elktownlabs/murgcam/web-backend/refphotos/low.jpeg

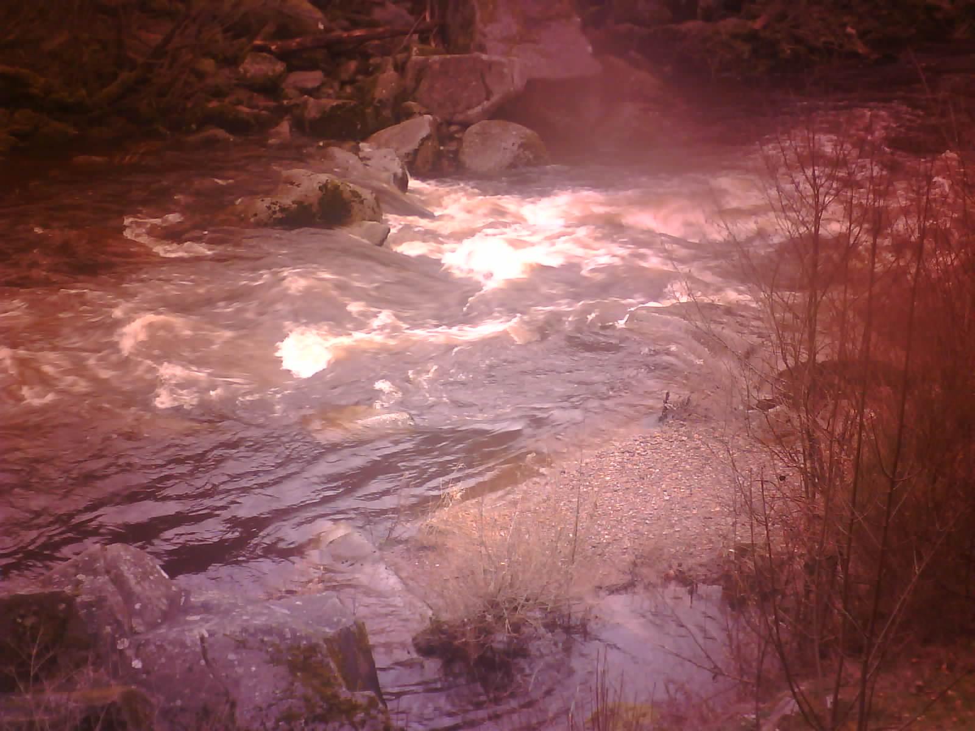
web-backend/refphotos/low.jpeg
