elktownlabs/murgcam/cad/optics/aliexpress-order-csmount-lens-holder.png

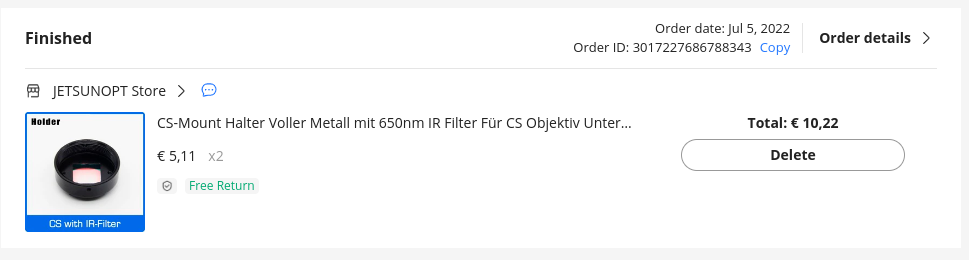
cad/optics/aliexpress-order-csmount-lens-holder.png
