elktownlabs/murgcam/cad/optics/aliexpress-order-csmount-zoom-lens.png

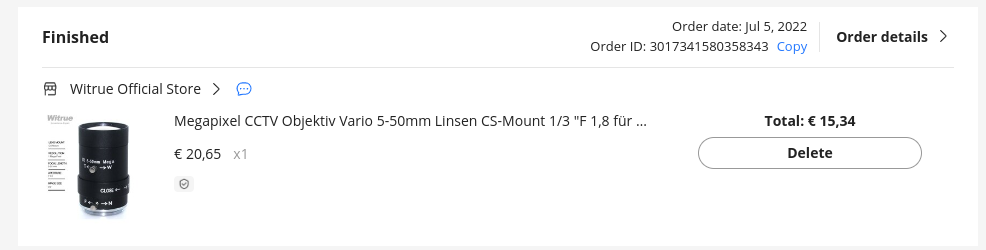
cad/optics/aliexpress-order-csmount-zoom-lens.png
