elktownlabs/murgcam/cad/enclosure_narrow/base_narrow_cam/bolts/common/version.scad

function BOLTS_version() = [0, 3, "LGPL 2.1+"];
function BOLTS_date() = [2014,4,24];
function BOLTS_license() = "LGPL 2.1+";
