elktownlabs/murgcam/firmware/elkcam_firmware/main/webserver.c

#include "webserver.h"
#include "esp_http_server.h"
#include "esp_log.h"
#include "events.h"
#include "gpios.h"
#include "cJSON.h"
#include "cam.h"
#include "camhandler.h"
#include "configstorage.h"

static const char *TAG = "httpserver";

unsigned char index_html_gz[] = {
  0x1f, 0x8b, 0x08, 0x08, 0xf7, 0x94, 0x00, 0x61, 0x00, 0x03, 0x69, 0x6e,
  0x64, 0x65, 0x78, 0x2e, 0x68, 0x74, 0x6d, 0x6c, 0x00, 0xed, 0x5c, 0x6d,
  0x73, 0xdb, 0x36, 0x12, 0xfe, 0x9e, 0x5f, 0x81, 0x32, 0x6d, 0x25, 0xf7,
  0x4c, 0x59, 0xb2, 0x9d, 0xc4, 0x91, 0x2d, 0xf5, 0x9c, 0x34, 0x77, 0xe9,
  0x4d, 0x9a, 0xf8, 0xea, 0xbe, 0xdc, 0x4d, 0xa7, 0xe3, 0x42, 0x24, 0x28,
  0xb1, 0x26, 0x09, 0x16, 0x00, 0x65, 0xbb, 0x19, 0xff, 0xf7, 0x5b, 0x00,
  0x24, 0x05, 0x50, 0xa0, 0x4c, 0xa5, 0xae, 0xa7, 0xbd, 0x3b, 0x69, 0x26,
  0x26, 0x09, 0xec, 0x2e, 0x76, 0xf7, 0xd9, 0xc5, 0x02, 0xa0, 0x72, 0xb2,
  0x10, 0x69, 0x32, 0x7d, 0x84, 0xd0, 0xc9, 0x82, 0xe0, 0x50, 0x5e, 0xc0,
  0x65, 0x4a, 0x04, 0x46, 0xc1, 0x02, 0x33, 0x4e, 0xc4, 0xc4, 0x2b, 0x44,
  0xe4, 0x1f, 0x79, 0x66, 0x53, 0x86, 0x53, 0x32, 0xf1, 0x96, 0x31, 0xb9,
  0xca, 0x29, 0x13, 0x1e, 0x0a, 0x68, 0x26, 0x48, 0x06, 0x5d, 0xaf, 0xe2,
  0x50, 0x2c, 0x26, 0x21, 0x59, 0xc6, 0x01, 0xf1, 0xd5, 0xcd, 0x6e, 0x9c,
  0xc5, 0x22, 0xc6, 0x89, 0xcf, 0x03, 0x9c, 0x90, 0xc9, 0xa8, 0xe2, 0x23,
  0x62, 0x91, 0x90, 0xe9, 0xab, 0xe4, 0x32, 0xc0, 0xe9, 0xc9, 0x9e, 0xbe,
  0xd3, 0x2d, 0x5c, 0xdc, 0x54, 0xd7, 0xf2, 0xb3, 0xf7, 0x59, 0x7d, 0xf9,
  0x19, 0x7a, 0x79, 0x7e, 0x8e, 0x22, 0xca, 0x90, 0x58, 0x10, 0x44, 0x78,
  0x7e, 0xb0, 0x8f, 0x80, 0x1c, 0x5d, 0x91, 0x19, 0x27, 0x6c, 0x49, 0xd8,
  0xaa, 0xe7, 0x5e, 0x7d, 0x39, 0xa3, 0xe1, 0x0d, 0x7a, 0x5f, 0xdf, 0x46,
  0x30, 0x54, 0x3f, 0xc2, 0x69, 0x9c, 0xdc, 0x8c, 0xd1, 0x29, 0x83, 0x91,
  0xed, 0xbe, 0x26, 0xc9, 0x92, 0x88, 0x38, 0xc0, 0xbb, 0x1c, 0x67, 0xdc,
  0x07, 0x56, 0x71, 0x74, 0xbc, 0xa2, 0xc7, 0xc1, 0xe5, 0x9c, 0xd1, 0x22,
  0x0b, 0xc7, 0xe8, 0xf1, 0xe8, 0x48, 0x7e, 0x57, 0x8d, 0x01, 0x4d, 0x28,
  0x83, 0xe7, 0xaf, 0xfe, 0x26, 0xbf, 0xc7, 0xb6, 0x14, 0x1e, 0xff, 0x4a,
  0xc6, 0x68, 0xf4, 0x34, 0xbf, 0xae, 0x9f, 0xdf, 0xd6, 0x57, 0xd8, 0x18,
  0x53, 0x1b, 0x17, 0x41, 0xae, 0x85, 0x1f, 0x92, 0x80, 0x32, 0x2c, 0x62,
  0x9a, 0x8d, 0x11, 0x0c, 0x82, 0xb0, 0x24, 0xce, 0x88, 0x83, 0xe1, 0x62,
  0xbf, 0xa9, 0x65, 0x29, 0xff, 0xc8, 0x29, 0x9f, 0x93, 0x40, 0xf2, 0x1c,
  0xa4, 0x38, 0xce, 0x0c, 0xc2, 0x30, 0xe6, 0x79, 0x82, 0xc1, 0x34, 0x51,
  0x42, 0x5c, 0x64, 0x8f, 0x53, 0x92, 0x15, 0xbb, 0x2d, 0xc4, 0x92, 0xc6,
  0x0f, 0x63, 0xa6, 0x5b, 0xc7, 0x52, 0xaf, 0x22, 0xcd, 0xda, 0xb8, 0xb8,
  0xa4, 0x66, 0x34, 0x23, 0xc7, 0x36, 0xbf, 0x2b, 0x86, 0x73, 0xd9, 0x20,
  0xff, 0xae, 0x9a, 0x14, 0xb6, 0xc6, 0xe8, 0xe0, 0x68, 0x98, 0x5f, 0xb7,
  0xf8, 0xea, 0xe0, 0xa9, 0xfc, 0xae, 0x1a, 0x73, 0x1c, 0x86, 0x71, 0x36,
  0x1f, 0xa3, 0x23, 0x8b, 0x84, 0x32, 0xb0, 0xa9, 0xcf, 0x70, 0x18, 0x17,
  0x7c, 0x8c, 0x0e, 0xcd, 0xb6, 0x14, 0xb3, 0x79, 0x9c, 0xf9, 0x82, 0xc2,
  0x00, 0xfc, 0xd1, 0xd0, 0xd1, 0xc4, 0xe2, 0xf9, 0x42, 0x80, 0x8d, 0xad,
  0xb6, 0x5b, 0x03, 0xbb, 0x5a, 0xdd, 0x32, 0x3e, 0xda, 0xec, 0xec, 0xd4,
  0xd8, 0xd6, 0x17, 0x27, 0xf1, 0x3c, 0xf3, 0x63, 0x41, 0x52, 0x18, 0x24,
  0x17, 0x8c, 0x88, 0x60, 0xe1, 0x10, 0x68, 0xe0, 0x3e, 0x8a, 0xe7, 0x05,
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
};
unsigned int index_html_gz_len = 3640;


/* An HTTP GET handler */
static esp_err_t photo_get_handler(httpd_req_t *req)
{
    char*  buf;
    size_t buf_len;

    /* Get header value string length and allocate memory for length + 1,
     * extra byte for null termination */
    buf_len = httpd_req_get_hdr_value_len(req, "Host") + 1;
    if (buf_len > 1) {
        buf = malloc(buf_len);
        /* Copy null terminated value string into buffer */
        if (httpd_req_get_hdr_value_str(req, "Host", buf, buf_len) == ESP_OK) {
            ESP_LOGI(TAG, "Host %s requested a picture.", buf);
        }
        free(buf);
    }


    uint8_t *cam_buf = NULL;

    ESP_LOGI(TAG, "Taking picture");
    reinit_cam();
    camhandler_load_config_from_nvs();
    cam_start();
    size_t data_len = cam_take(&cam_buf, 8000 / portTICK_PERIOD_MS);
    cam_stop();
    if (data_len == 0) {
        ESP_LOGE(TAG, "Camera timed out");
        cam_give(cam_buf);
        return ESP_OK;
    }
    /* find end of jpeg stream and truncate data there */
    for (uint32_t i=0; i<data_len-1; i++) {
        if (cam_buf[i] == 0xff && cam_buf[i+1] == 0xd9) {
            ESP_LOGI(TAG, "Shortened data from %d to %d.", data_len, i+2);
            data_len = i+2;
            break;
        }
    }
    ESP_LOGI(TAG, "Picture taken. Size = %d", data_len);

    /* Set some custom headers */
    httpd_resp_set_hdr(req, "Content-Type", "image/jpeg");

    /* Send response with custom headers and body set as the
     * string passed in user context*/
    httpd_resp_send(req, (const char*)cam_buf, data_len);

    cam_give(cam_buf);

    /* After sending the HTTP response the old HTTP request
     * headers are lost. Check if HTTP request headers can be read now. */
    if (httpd_req_get_hdr_value_len(req, "Host") == 0) {
        ESP_LOGI(TAG, "Request headers lost");
    }
    return ESP_OK;
}


/* HTTP GET handler for root page (/) */
static esp_err_t index_handler(httpd_req_t *req)
{
    char*  buf;
    size_t buf_len;

    /* Get header value string length and allocate memory for length + 1,
     * extra byte for null termination */
    buf_len = httpd_req_get_hdr_value_len(req, "Host") + 1;
    if (buf_len > 1) {
        buf = malloc(buf_len);
        /* Copy null terminated value string into buffer */
        if (httpd_req_get_hdr_value_str(req, "Host", buf, buf_len) == ESP_OK) {
            ESP_LOGI(TAG, "Host %s requested index.", buf);
        }
        free(buf);
    }

    /* Set some custom headers */
    httpd_resp_set_hdr(req, "Content-Type", "text/html");
    httpd_resp_set_hdr(req, "Content-Encoding" , "gzip");

    httpd_resp_send(req, (const char*)index_html_gz, index_html_gz_len);


    /* After sending the HTTP response the old HTTP request
     * headers are lost. Check if HTTP request headers can be read now. */
    if (httpd_req_get_hdr_value_len(req, "Host") == 0) {
        ESP_LOGI(TAG, "Request headers lost");
    }

    return ESP_OK;
}


/* An HTTP GET handler */
static esp_err_t config_get_handler(httpd_req_t *req)
{
    char*  buf;
    size_t buf_len;
	cJSON *root;

    /* build json configuration */
    root = cJSON_CreateObject();
    camera_config_t* cam_conf = config_cam();
    cell_config_t* cell_conf = config_cell();
    system_config_t* sys_conf = config_system();
    cJSON_AddNumberToObject(root, "cam_quality", cam_conf->quality);
    cJSON_AddNumberToObject(root, "cam_auto_exposure", cam_conf->auto_exposure);
    cJSON_AddNumberToObject(root, "cam_light_mode", cam_conf->light_mode);
    cJSON_AddNumberToObject(root, "cam_color_saturation", cam_conf->color_saturation);
    cJSON_AddNumberToObject(root, "cam_pixeltiming", cam_conf->pixeltiming);
    cJSON_AddNumberToObject(root, "cam_brightness", cam_conf->brightness);
    cJSON_AddNumberToObject(root, "cam_hue", cam_conf->hue);
    cJSON_AddNumberToObject(root, "cam_sharpness", cam_conf->sharpness);
    cJSON_AddNumberToObject(root, "cam_contrast", cam_conf->contrast);
    cJSON_AddStringToObject(root, "cell_pin", cell_conf->pin);
    cJSON_AddStringToObject(root, "cell_apn", cell_conf->apn);
    cJSON_AddStringToObject(root, "cell_apn_user", cell_conf->apn_user);
    cJSON_AddStringToObject(root, "cell_apn_pass", cell_conf->apn_pass);
    cJSON_AddNumberToObject(root, "cell_apn_auth", cell_conf->apn_auth);
    cJSON_AddStringToObject(root, "cell_remote_address", cell_conf->remote_address);
    cJSON_AddStringToObject(root, "cell_remote_url", cell_conf->remote_url);
    cJSON_AddNumberToObject(root, "sys_secs_between_photos", sys_conf->secs_between_photos);
    cJSON_AddNumberToObject(root, "sys_minimum_voltage", sys_conf->min_voltage);

    /* Get header value string length and allocate memory for length + 1,
     * extra byte for null termination */
    buf_len = httpd_req_get_hdr_value_len(req, "Host") + 1;
    if (buf_len > 1) {
        buf = malloc(buf_len);
        /* Copy null terminated value string into buffer */
        if (httpd_req_get_hdr_value_str(req, "Host", buf, buf_len) == ESP_OK) {
            ESP_LOGI(TAG, "Host %s requested configuration.", buf);
        }
        free(buf);
    }

    /* Set some custom headers */
    httpd_resp_set_hdr(req, "Content-Type", "application/json");

    /* Send response with custom headers and body set as the
     * string passed in user context*/
    const char *my_json_string = cJSON_Print(root);
    httpd_resp_send(req, my_json_string, strlen(my_json_string));

    /* free memory */
    cJSON_Delete(root);

    /* After sending the HTTP response the old HTTP request
     * headers are lost. Check if HTTP request headers can be read now. */
    if (httpd_req_get_hdr_value_len(req, "Host") == 0) {
        ESP_LOGI(TAG, "Request headers lost");
    }

    return ESP_OK;
}



/* An HTTP GET handler */
static esp_err_t config_set_handler(httpd_req_t *req)
{
    char content[512];

    /* truncate if content length larger than the buffer */
    size_t recv_size = (req->content_len < sizeof(content)) ? req->content_len : sizeof(content);

    int ret = httpd_req_recv(req, content, recv_size);
    if (ret <= 0) {  /* 0 return value indicates connection closed */
        /* Check if timeout occurred */
        if (ret == HTTPD_SOCK_ERR_TIMEOUT) {
            httpd_resp_send_408(req);
        }
        return ESP_FAIL;
    }

    ESP_LOGI(TAG, "Received set request: %s", content);

    /* parse json */
    cJSON *config_json = cJSON_Parse(content);
    if (config_json == NULL) {
        ESP_LOGE(TAG, "Error parsing json in setconfig post request");
        httpd_resp_send_408(req);
        return ESP_FAIL;
    }

    /* update config storage */
    camera_config_t cam_conf = *(config_cam());
    system_config_t sys_conf = *(config_system());
    cell_config_t cell_conf = *(config_cell());

    cJSON *value;
    value = cJSON_GetObjectItemCaseSensitive(config_json, "cam_quality");
    if (cJSON_IsNumber(value)) {
        ESP_LOGI(TAG, "Setting quality to %d", value->valueint);
        cam_conf.quality = value->valueint;
    }
    value = cJSON_GetObjectItemCaseSensitive(config_json, "cam_auto_exposure");
    if (cJSON_IsNumber(value)) {
        ESP_LOGI(TAG, "Setting auto exposure to %d", value->valueint);
        cam_conf.auto_exposure = value->valueint;
    }
    value = cJSON_GetObjectItemCaseSensitive(config_json, "cam_light_mode");
    if (cJSON_IsNumber(value)) {
        ESP_LOGI(TAG, "Setting light mode to %d", value->valueint);
        cam_conf.light_mode = value->valueint;
    }
    value = cJSON_GetObjectItemCaseSensitive(config_json, "cam_color_saturation");
    if (cJSON_IsNumber(value)) {
        ESP_LOGI(TAG, "Setting saturation to %d", value->valueint);
        cam_conf.color_saturation = value->valueint;
    }
    value = cJSON_GetObjectItemCaseSensitive(config_json, "cam_pixeltiming");
    if (cJSON_IsNumber(value)) {
        ESP_LOGI(TAG, "Setting pixel timing to %d", value->valueint);
        cam_conf.pixeltiming = value->valueint;
    }
    value = cJSON_GetObjectItemCaseSensitive(config_json, "cam_brightness");
    if (cJSON_IsNumber(value)) {
        ESP_LOGI(TAG, "Setting brightness to %d", value->valueint);
        cam_conf.brightness = value->valueint;
    }
    value = cJSON_GetObjectItemCaseSensitive(config_json, "cam_contrast");
    if (cJSON_IsNumber(value)) {
        ESP_LOGI(TAG, "Setting contrast to %d", value->valueint);
        cam_conf.contrast = value->valueint;
    }
    value = cJSON_GetObjectItemCaseSensitive(config_json, "cam_hue");
    if (cJSON_IsNumber(value)) {
        ESP_LOGI(TAG, "Setting hue to %d", value->valueint);
        cam_conf.hue = value->valueint;
    }
    value = cJSON_GetObjectItemCaseSensitive(config_json, "cam_sharpness");
    if (cJSON_IsNumber(value)) {
        ESP_LOGI(TAG, "Setting sharpness to %d", value->valueint);
        cam_conf.sharpness = value->valueint;
    }
    value = cJSON_GetObjectItemCaseSensitive(config_json, "cell_pin");
    if (cJSON_IsString(value)) {
        ESP_LOGI(TAG, "Setting cell pin to %s", value->valuestring);
        strncpy(cell_conf.pin, value->valuestring, sizeof(cell_conf.pin));
    }
    value = cJSON_GetObjectItemCaseSensitive(config_json, "cell_apn");
    if (cJSON_IsString(value)) {
        ESP_LOGI(TAG, "Setting cell apn to %s", value->valuestring);
        strncpy(cell_conf.apn, value->valuestring, sizeof(cell_conf.apn));
    }
    value = cJSON_GetObjectItemCaseSensitive(config_json, "cell_apn_user");
    if (cJSON_IsString(value)) {
        ESP_LOGI(TAG, "Setting cell apn user to %s", value->valuestring);
        strncpy(cell_conf.apn_user, value->valuestring, sizeof(cell_conf.apn_user));
    }
    value = cJSON_GetObjectItemCaseSensitive(config_json, "cell_apn_pass");
    if (cJSON_IsString(value)) {
        ESP_LOGI(TAG, "Setting cell apn password to %s", value->valuestring);
        strncpy(cell_conf.apn_pass, value->valuestring, sizeof(cell_conf.apn_pass));
    }
    value = cJSON_GetObjectItemCaseSensitive(config_json, "cell_apn_auth");
    if (cJSON_IsNumber(value)) {
        ESP_LOGI(TAG, "Setting apn auth method to %d", value->valueint);
        cell_conf.apn_auth = value->valueint;
    }
    value = cJSON_GetObjectItemCaseSensitive(config_json, "cell_remote_address");
    if (cJSON_IsString(value)) {
        ESP_LOGI(TAG, "Setting remote address to %s", value->valuestring);
        strncpy(cell_conf.remote_address, value->valuestring, sizeof(cell_conf.remote_address));
    }
    value = cJSON_GetObjectItemCaseSensitive(config_json, "cell_remote_url");
    if (cJSON_IsString(value)) {
        ESP_LOGI(TAG, "Setting remote url to %s", value->valuestring);
        strncpy(cell_conf.remote_url, value->valuestring, sizeof(cell_conf.remote_url));
    }
    value = cJSON_GetObjectItemCaseSensitive(config_json, "sys_secs_between_photos");
    if (cJSON_IsNumber(value)) {
        ESP_LOGI(TAG, "Setting secs between photos to %d", value->valueint);
        sys_conf.secs_between_photos = value->valueint;
    }
    value = cJSON_GetObjectItemCaseSensitive(config_json, "sys_minimum_voltage");
    if (cJSON_IsNumber(value)) {
        ESP_LOGI(TAG, "Setting minimum voltage to %d", value->valueint);
        sys_conf.min_voltage = value->valueint;
    }

    config_write_values(&sys_conf, &cell_conf, &cam_conf);
    ESP_LOGI(TAG, "Saved values to storage");
    config_load_values();

    /* send response */
    const char resp[] = "success";
    httpd_resp_send(req, resp, HTTPD_RESP_USE_STRLEN);

    /* After sending the HTTP response the old HTTP request
     * headers are lost. Check if HTTP request headers can be read now. */
    if (httpd_req_get_hdr_value_len(req, "Host") == 0) {
        ESP_LOGI(TAG, "Request headers lost");
    }
    return ESP_OK;
}


static const httpd_uri_t photo = {
    .uri       = "/photo",
    .method    = HTTP_GET,
    .handler   = photo_get_handler,
    /* Let's pass response string in user
     * context to demonstrate it's usage */
    .user_ctx  = 0x00
};

static const httpd_uri_t config_get = {
    .uri       = "/getconfig",
    .method    = HTTP_GET,
    .handler   = config_get_handler,
    /* Let's pass response string in user
     * context to demonstrate it's usage */
    .user_ctx  = 0x00
};

static const httpd_uri_t config_set = {
    .uri       = "/setconfig",
    .method    = HTTP_POST,
    .handler   = config_set_handler,
    /* Let's pass response string in user
     * context to demonstrate it's usage */
    .user_ctx  = 0x00
};

static const httpd_uri_t index_html = {
    .uri       = "/",
    .method    = HTTP_GET,
    .handler   = index_handler,
    /* Let's pass response string in user
     * context to demonstrate it's usage */
    .user_ctx  = 0x00
};


httpd_handle_t start_webserver(void)
{
    httpd_handle_t server = NULL;
    httpd_config_t config = HTTPD_DEFAULT_CONFIG();
    /*config.recv_wait_timeout = 30;
    config.send_wait_timeout = 30;*/

    // Start the httpd server
    ESP_LOGI(TAG, "Starting server on port: '%d'", config.server_port);
    if (httpd_start(&server, &config) == ESP_OK) {
        // Set URI handlers
        ESP_LOGI(TAG, "Registering URI handlers");
        httpd_register_uri_handler(server, &photo);
        httpd_register_uri_handler(server, &config_get);
        httpd_register_uri_handler(server, &config_set);
        httpd_register_uri_handler(server, &index_html);
        return server;
    }

    ESP_LOGI(TAG, "Error starting server!");
    return NULL;
}


void stop_webserver(httpd_handle_t server)
{
    // Stop the httpd server
    httpd_stop(server);
}
